jhonattanrivera/wifikit/HTTP_Server/HTTP_Server+Panel/server/img/android-desktop.png

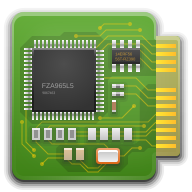
HTTP_Server/HTTP_Server+Panel/server/img/android-desktop.png
