jhonattanrivera/wifikit/pictures/IMG_1017.jpg

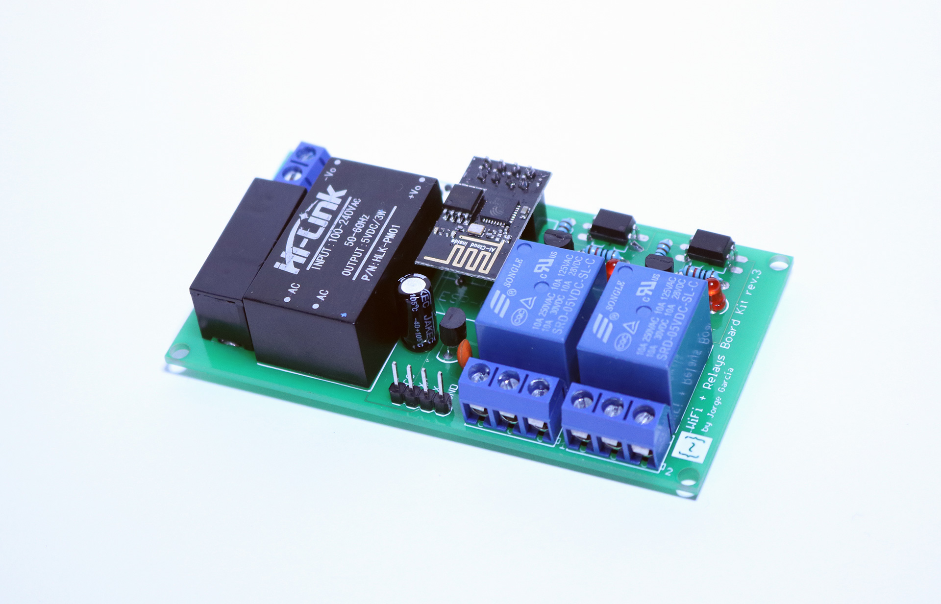
pictures/IMG_1017.jpg
