jhonattanrivera/wifikit/pictures/IMG_1021.jpg

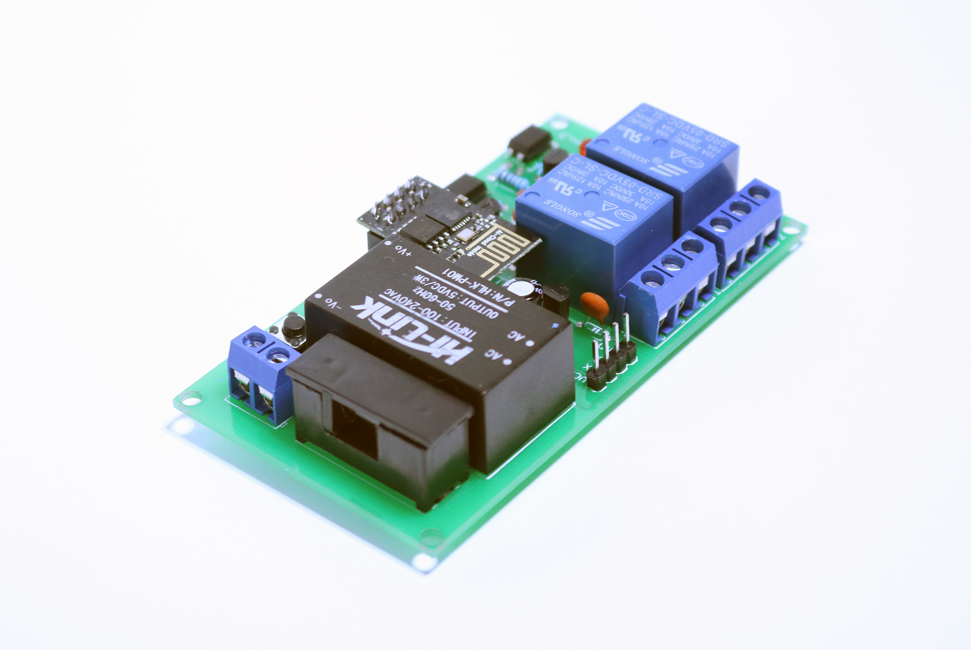
pictures/IMG_1021.jpg
