jhonattanrivera/wifikit/pictures/IMG_1026.jpg

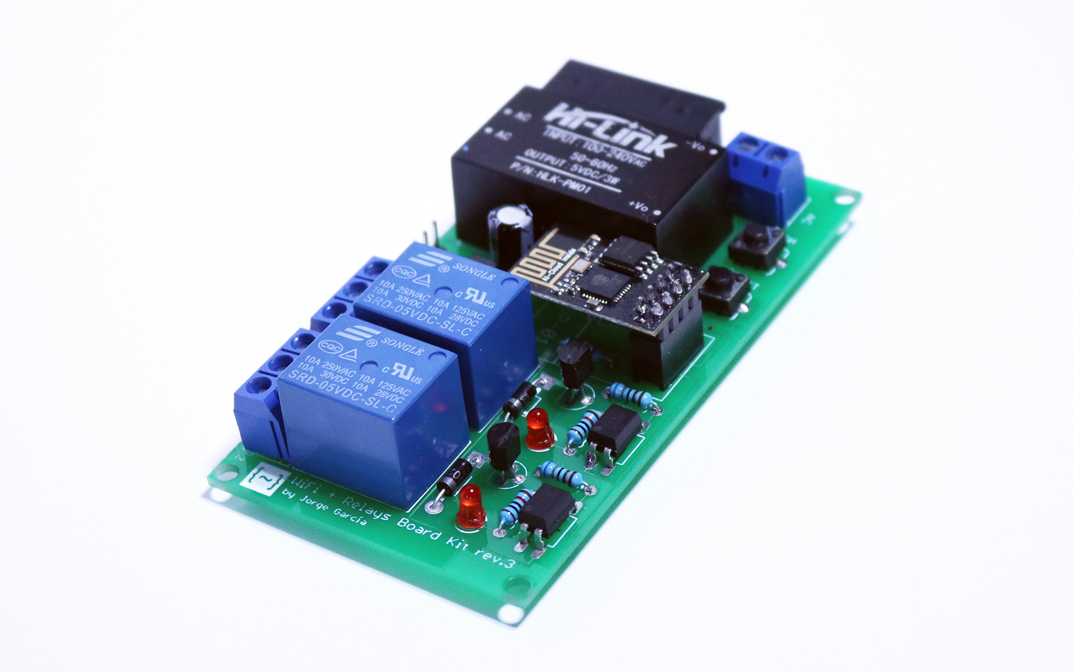
pictures/IMG_1026.jpg
