jhonattanrivera/wifikit/schematics/WiFi + Relays Board Kit.sch

## EAGLE design schematics/WiFi + Relays Board Kit.sch (2017-04-13)

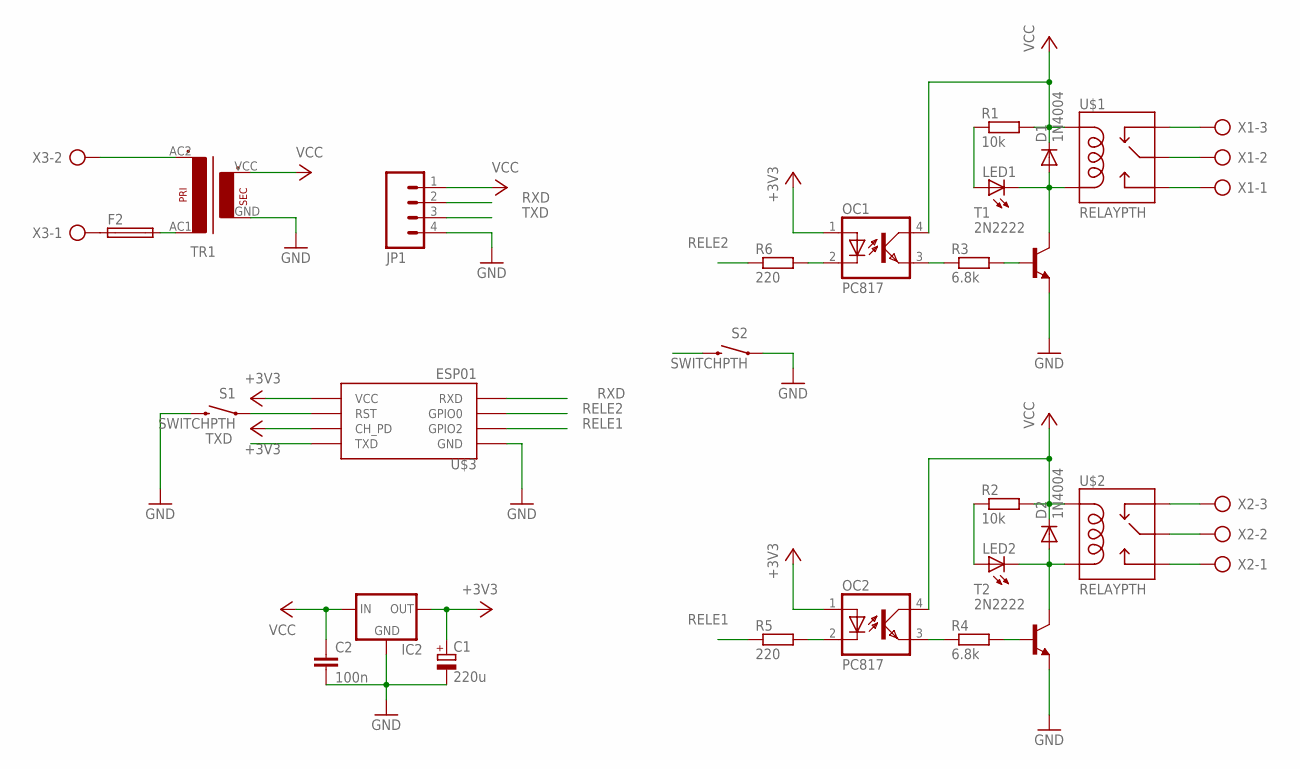
[picture p8: schematic WiFi + Relays Board Kit.sch]

Parts:
C1: 220u; E2,5-6
C2: 100n; C050-024X044
D1, D2: 1N4004; DO41-10
F2: SH22,5A
IC2: MCP1700TRI; TO92
JP1: M04PTH; 1X04
LED1, LED2: LED3MM
OC1, OC2: PC817; DIL04
R1, R2: 10k; 0204/7
R3, R4: 6.8k; 0204/7
R5, R6: 220; 0204/7
S1, S2: SWITCHPTH; TACTILE-PTH
T1, T2: 2N2222; TO92-EBC-OVAL
TR1: HLK-PM01
U$1, U$2: RELAYPTH; SRD-05VDC-SL-C
U$3: ESP01
X1, X2: AK500/3
X3: AK500/2

Connections:
+3V3: C1.+, IC2.3 (OUT), OC1.1 (A), OC2.1 (A), U$3.CH_PD, U$3.VCC
GND: C1.-, C2.2, IC2.1 (GND), JP1.4, S1.3 (2), S2.1, T1.E, T2.E, TR1.GND (S4), U$3.GND
unnamed: D1.A, LED1.K (C), T1.C, U$1.COIL0
unnamed: D2.A, LED2.K (C), T2.C, U$2.COIL0
unnamed: LED1.A, R1.1
unnamed: LED2.A, R2.1
unnamed: OC1.3 (EMIT), R3.1
unnamed: R3.2, T1.B
unnamed: S1.1, U$3.RST
unnamed: U$1.SWCLOSED (SWCLOSE), X1.3
unnamed: U$1.SWCOMMON, X1.2
unnamed: U$1.SWOPEN, X1.1
unnamed: U$2.SWCLOSED (SWCLOSE), X2.3
unnamed: U$2.SWCOMMON, X2.2
unnamed: U$2.SWOPEN, X2.1
unnamed: OC2.2 (C), R5.2
unnamed: F2.1, X3.1
unnamed: OC2.3 (EMIT), R4.1
unnamed: R4.2, T2.B
unnamed: OC1.2 (C), R6.2
unnamed: TR1.AC2 (P2), X3.2
unnamed: F2.2, TR1.AC1 (P1)
RELE1: R5.1, U$3.GPIO2
RELE2: R6.1, S2.3 (2), U$3.GPIO0
RXD: JP1.2, U$3.RX (RXD)
TXD: JP1.3, U$3.TX (TXD)
VCC: C2.1, D1.C, D2.C, IC2.2 (IN), JP1.1, OC1.4 (COL), OC2.4 (COL), R1.2, R2.2, TR1.VCC (S3), U$1.COIL1, U$2.COIL1
